spirit0908/STM32/boards/03_can2uart_converter/PCB/can_uart_converter.sch

## KiCad design boards/03_can2uart_converter/PCB/can_uart_converter.sch (2021-06-02)

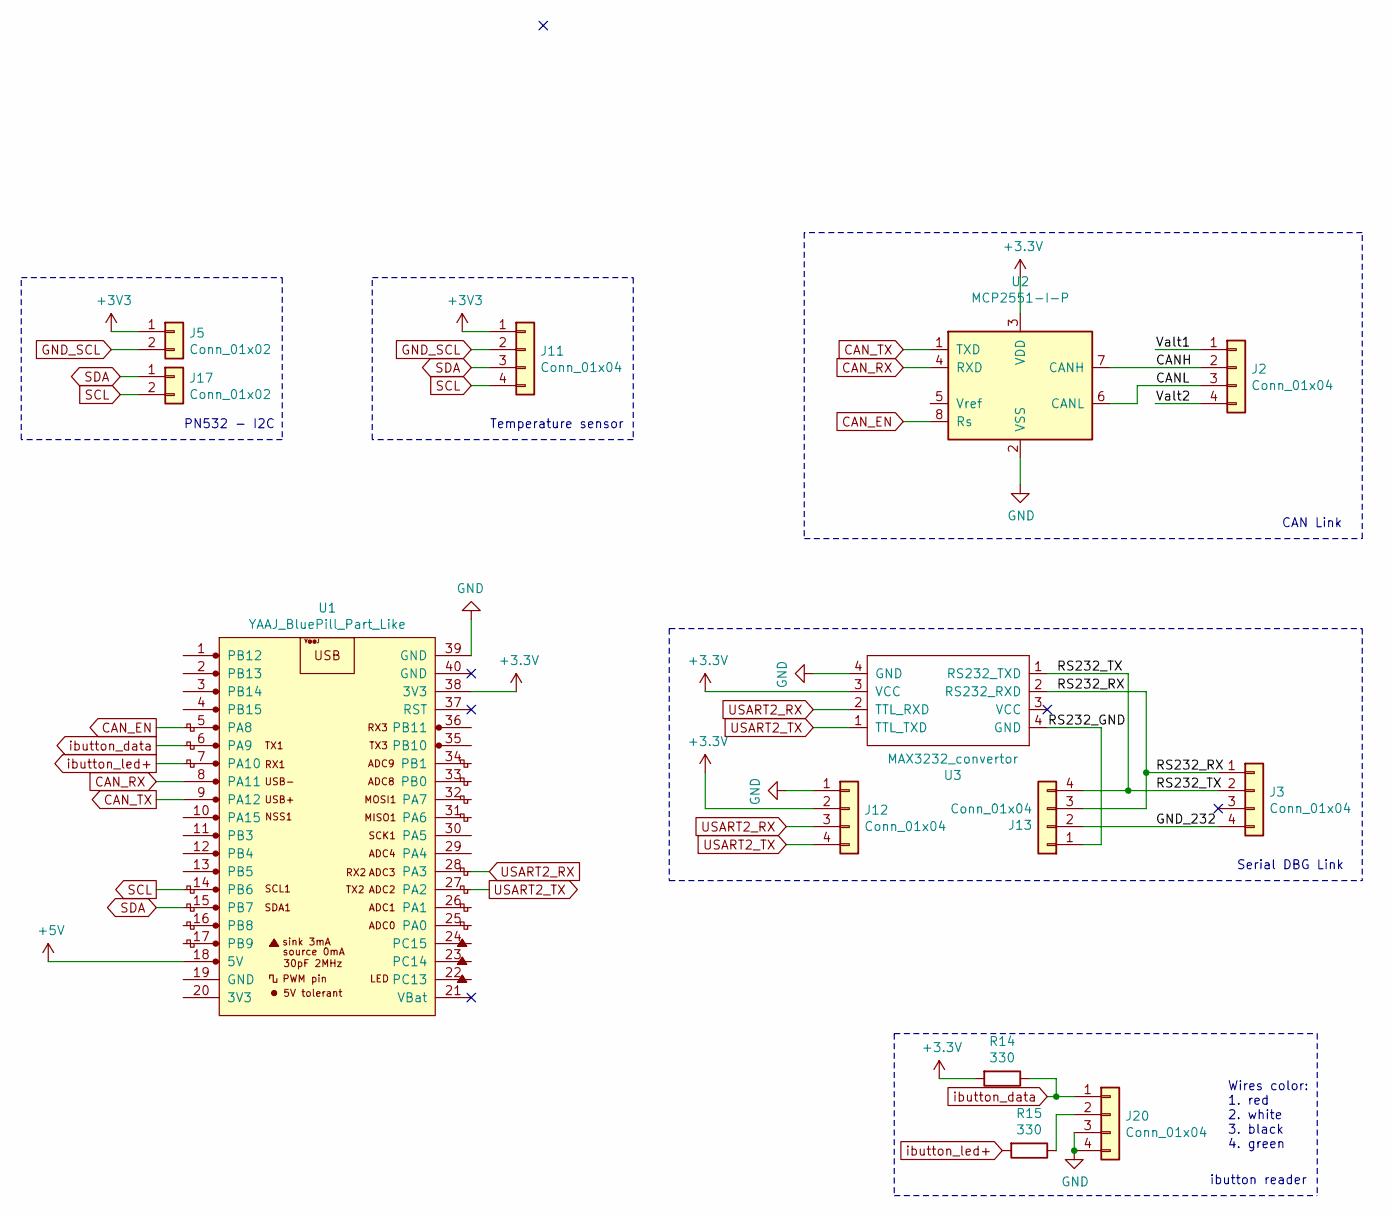
[picture p13: schematic can_uart_converter.sch]

Parts:
J2: Conn_01x04; PinHeader_1x04_P2.54mm_Horizontal
J3, J11, J12, J13, J20: Conn_01x04; PinHeader_1x04_P2.54mm_Vertical
J5, J17: Conn_01x02; PinHeader_1x02_P2.54mm_Vertical
R14, R15: 330; R_Axial_DIN0204_L3.6mm_D1.6mm_P7.62mm_Horizontal
U1: YAAJ_BluePill_Part_Like; YAAJ_BluePill_1
U2: MCP2551-I-P; DIP-8_W7.62mm
U3: MAX3232_convertor

Connections:
+3.3V: J12.2, R14.2, U1.38 (3V3), U2.3 (VDD), U3.3 (VCC)
+3V3: J5.1, J11.1
+5V: U1.18 (5V)
CANH: J2.2, U2.7 (CANH)
CANL: J2.3, U2.6 (CANL)
CAN_EN: U1.5 (PA8), U2.8 (Rs)
CAN_RX: U1.8 (PA11), U2.4 (RXD)
CAN_TX: U1.9 (PA12), U2.1 (TXD)
GND: J12.1, J20.3, J20.4, U1.39 (GND), U2.2 (VSS), U3.4 (GND)
GND_232: J3.4, J13.2
GND_SCL: J5.2, J11.2
unnamed: J20.2, R15.1
RS232_GND: J13.1, U3.4 (GND)
RS232_RX: J3.1, J13.3, U3.2 (RS232_RXD)
RS232_TX: J3.2, J13.4, U3.1 (RS232_TXD)
SCL: J11.4, J17.2, U1.14 (PB6)
SDA: J11.3, J17.1, U1.15 (PB7)
USART2_RX: J12.3, U1.28 (PA3), U3.2 (RS232_RXD)
USART2_TX: J12.4, U1.27 (PA2), U3.1 (RS232_TXD)
Valt1: J2.1
Valt2: J2.4
ibutton_data: J20.1, R14.1, U1.6 (PA9)
ibutton_led+: R15.2, U1.7 (PA10)

Notes on the sheet:
Serial DBG Link
CAN Link
PN532 - I2C
Temperature sensor
ibutton reader
Wires color: 1. red 2. white 3. black 4. green
