spirit0908/STM32/boards/03_can2uart_converter/PCB/ressources.sch

## KiCad design boards/03_can2uart_converter/PCB/ressources.sch (2020-12-13)

Schematic: ressources.sch

Parts:
BZ2: Buzzer; Buzzer_12x9.5RM7.6
J21, J23, J27, J28, J35: Conn_01x02; PinHeader_1x02_P2.54mm_Vertical
J22, J25, J29, J30, J31, J32, J34: Conn_01x04; PinHeader_1x04_P2.54mm_Vertical
J24, J26: Conn_01x03; PinHeader_1x03_P2.54mm_Vertical
J33: DB9_Female; DSUB-9_Female_Horizontal_P2.77x2.84mm_EdgePinOffset4.94mm_H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
J36: Conn_01x04; PinHeader_1x04_P2.54mm_Horizontal
R16, R17, R18, R19, R22, R23, R24: 330; R_Axial_DIN0204_L3.6mm_D1.6mm_P7.62mm_Horizontal
R20: 1.2k; R_Axial_DIN0204_L3.6mm_D1.6mm_P7.62mm_Horizontal
R21: 10k; R_Axial_DIN0204_L3.6mm_D1.6mm_P5.08mm_Horizontal
U10, U11, U12, U13: 4N25; DIP-6_W7.62mm
U14: LTV-814; DIP-4_W7.62mm
U15: MAX3232_convertor
U16: MCP2551-I-P; DIP-8_W7.62mm

Notes on the sheet:
Serial DBG Link
EDF Teleinfo
CAN Link
PN532 - I2C
LED STRIP WHITE
Buzzer
External connectors
Temperature sensor
LED STRIP RGB
Wires color: 1. red 2. white 3. black 4. green
ibutton reader
