spirit0908/STM32/modules/Teleinfo/teleinfo.c

/********************************************************************************
 * File Name          : teleinfo.c
 * Date               : 10/08/2007
 * Description        : Main program body
 *******************************************************************************/

/************************************************************************
* INCLUDES *
************************************************************************/
#include "stm32f10x_lib.h"

#include "stm32f10x_flash.h"
#include "stm32f10x_gpio.h"
#include "stm32f10x_map.h"
#include "stm32f10x_nvic.h"
#include "stm32f10x_rcc.h"
#include "stm32f10x_type.h"
#include "Fifo.h"
#include "teleinfo.h"

/************************************************************************
* DEFINES *
************************************************************************/
#define TIC_FIFO_LENGTH     55

#define MODE1 1
#define MODE2 2
#define TIC_CRC_MODE MODE1


/************************************************************************
* GLOBAL VARIABLES *
************************************************************************/
unsigned char TIC_FIFO_Buff[TIC_FIFO_LENGTH][30];
unsigned char IinstMax=0;

u8 rawDataTab[170];
u16 cptRawData=0;
u8 cptTIC_label=0;

T_TIC_INFO TIC_info;
T_TIC_FIFO TIC_Fifo;

/************************************************************************
* FUNCTIONS *
************************************************************************/

/************************************************************************
 * Function Name  : teleinfo_Init                                       *
 * Input          : None                                                *
 * Output         : None                                                *
 * Return         : None                                                *
 * Description    : Initialize TIC FIFO                                 *
 ************************************************************************/
void teleinfo_Init(void)
{
    /* Initialize Fifo */
    TIC_Fifo.buff       = &(TIC_FIFO_Buff[0][0]);
    TIC_Fifo.size       = TIC_FIFO_LENGTH;
    TIC_Fifo.WriteIdx   = 0;
    TIC_Fifo.ReadIdx    = 0;
    TIC_Fifo.NumElem    = 0;
    TIC_Fifo.NumMaxElem = 0;
    TIC_Fifo.overrun    = 0;
}

/************************************************************************
 * Function Name  : teleinfo_Init                                       *
 * Input          : None                                                *
 * Output         : None                                                *
 * Return         : None                                                *
 * Description    : Initialize TIC FIFO                                 *
 ************************************************************************/
void teleinfo_TIC_reset_values(void)
{
    unsigned char resetStr[13]="-------------";

    /* Reset all options */
    TIC_set_option(ADCO,     resetStr, ADCO_LEN);
    TIC_set_option(OPTARIF,  resetStr, OPTARIF_LEN);
    TIC_set_option(ISOUSC,   resetStr, ISOUSC_LEN);
#if( CBEMM_BASE )
    TIC_set_option(BASE,     resetStr, BASE_LEN);
#endif
#if( CBEMM_HC )
    TIC_set_option(HCHC,     resetStr, HCHC_LEN);
    TIC_set_option(HCHP,     resetStr, HCHP_LEN);
#endif
#if( CBEMM_EJP )
    TIC_set_option(EJPHN,    resetStr, EJPHN_LEN);
    TIC_set_option(EJPHPM,   resetStr, EJPHPM_LEN);
    TIC_set_option(PEJP,     resetStr, PEJP_LEN);
#endif
#if( CBEMM_TEMPO )
    TIC_set_option(BBRHCJB,  resetStr, BBRHCJB_LEN);
    TIC_set_option(BBRHPJB,  resetStr, BBRHPJB_LEN);
    TIC_set_option(BBRHCJW,  resetStr, BBRHCJW_LEN);
    TIC_set_option(BBRHPJW,  resetStr, BBRHPJW_LEN);
    TIC_set_option(BBRHCJR,  resetStr, BBRHCJR_LEN);
    TIC_set_option(BBRHPJR,  resetStr, BBRHPJR_LEN);
    TIC_set_option(DEMAIN,   resetStr, DEMAIN_LEN);
#endif
    TIC_set_option(PTEC,     resetStr, PTEC_LEN);
    TIC_set_option(IINST,    resetStr, IINST_LEN);
    TIC_set_option(ADPS,     resetStr, ADPS_LEN);
    TIC_set_option(IMAX,     resetStr, IMAX_LEN);
    TIC_set_option(PAPP,     resetStr, PAPP_LEN);
    TIC_set_option(HHPHC,    resetStr, HHPHC_LEN);
    TIC_set_option(MOTDETAT, resetStr, MOTDETAT_LEN);
#if( CBETM )
    TIC_set_option(IINST1,   resetStr, IINST1_LEN);
    TIC_set_option(IINST2,   resetStr, IINST2_LEN);
    TIC_set_option(IINST3,   resetStr, IINST3_LEN);
    TIC_set_option(IMAX1,    resetStr, IMAX1_LEN);
    TIC_set_option(IMAX2,    resetStr, IMAX2_LEN);
    TIC_set_option(IMAX3,    resetStr, IMAX3_LEN);
    TIC_set_option(PMAX,     resetStr, PMAX_LEN);
#endif
#if( CBETM_SHORT )
    TIC_set_option(ADIR1,    resetStr, ADIR1_LEN);
    TIC_set_option(ADIR2,    resetStr, ADIR2_LEN);
    TIC_set_option(ADIR3,    resetStr, ADIR3_LEN);
#endif
#if( C_GAZ_AUTRE )
    TIC_set_option(GAZ,      resetStr, GAZ_LEN);
    TIC_set_option(AUTRE,    resetStr, AUTRE_LEN);
#endif
}

/********************************************************************************
 * Function Name  : teleinfo_rawByte_receive                                    *
 * Input          : None                                                        *
 * Output         : None                                                        *
 * Return         : None                                                        *
 * Description    : Add each raw byte received from the TIC device in the FIFO  *
 *                  and split the differents TIC messages. Each element of the  *
 *                  FIFO contain one label with its associated data.            *
 *******************************************************************************/
int teleinfo_rawByte_receive(u8 rawByte)
{
    switch(rawByte)
    {
        case ASCII_LF: /* Start of Label */
            cptTIC_label=0;
            TIC_FIFO_Buff[TIC_Fifo.WriteIdx][cptTIC_label++] = rawByte;
          break;

        case ASCII_CR: /* CR End of label */
          //store and increment fifo
          TIC_FIFO_Buff[TIC_Fifo.WriteIdx][cptTIC_label] = rawByte;

          TIC_Fifo.NumElem++;
          if(TIC_Fifo.NumElem > TIC_Fifo.NumMaxElem ) // For debug purpose
          {
              TIC_Fifo.NumMaxElem = TIC_Fifo.NumElem;
          }

          TIC_Fifo.WriteIdx++;
          if(TIC_Fifo.WriteIdx>=TIC_FIFO_LENGTH)
          {
            TIC_Fifo.WriteIdx=0;
          }
          break;

        case ASCII_STX: //STX Start of Transmission
        case ASCII_ETX: //ETX End of Transmission - !!! if last character was not a CR, label transmission is not complete (telereport access on-going)
          break;

        default:
          //store car
          TIC_FIFO_Buff[TIC_Fifo.WriteIdx][cptTIC_label++] = rawByte;
          break;
    }

    //temporary added for debug:
    if( (rawByte == ASCII_ETX) /*&& (TIC_Fifo.WriteIdx > 30)*/ )
    {
        Teleinfo_Mgt();
    }

    return 0;
}

/********************************************************************************
 * Function Name  : Teleinfo_Mgt                                                *
 * Input          : None                                                        *
 * Output         : None                                                        *
 * Return         : None                                                        *
 * Description    : Check validity for each record of the FIFO                  *
 *******************************************************************************/
void Teleinfo_Mgt(void)
{
    unsigned char label;
    unsigned long int value=0;
    unsigned char WriteIdx = TIC_Fifo.WriteIdx;
    unsigned char *ReadIdx = &(TIC_Fifo.ReadIdx);

    while(*ReadIdx != WriteIdx)
    {
        //check string validity and split values
        if( TIC_check_frame(TIC_FIFO_Buff[*ReadIdx], &label, &value ) )
        {
          //Frame is valid, update info
          if( label != INVALID )
          {
              (void)TIC_FillInInfo(label, value);
          }
        }
        else
        {
            //ignore frame
        }

        // Manage Fifo
        if(TIC_Fifo.NumElem>0)
        {
            TIC_Fifo.NumElem--;
        }

        /* Increment fifo index */
        TIC_Fifo.ReadIdx++;
        if(TIC_Fifo.ReadIdx>=TIC_FIFO_LENGTH)
        {
            TIC_Fifo.ReadIdx=0;
        }
    }
}

/********************************************************************************
 * Function Name  : TIC_check_frame                                             *
 * Input          : str[30]: TIC record in ASCII format                         *
 * Output         : labelCode: label of the record                              *
 *                  valueCode: value of the record                              *
 * Return         : validity of the record:                                     *
 *                   FALSE: record is invalid, record is discarded              *
 *                   TRUE: record is valid and the treatment is done            *
 * Description    : Check validity of a TIC record and split the label and the  *
 *                  value.                                                      *
 *******************************************************************************/
unsigned char TIC_check_frame(unsigned char str[30], unsigned char *labelCode, unsigned long int *labelValue)
{
    unsigned char strLen=0, i, tmp;
    unsigned char labelStr[10], valueStr[12], CRC;
    unsigned char labelLen=0, valueLen=0;

    unsigned char IsValid=FALSE;

    //Read each line received
    if( str[strLen++] == ASCII_LF ) //Check line begins with LF
    {
        /* Get label */
        do
        {
            labelStr[labelLen++] = str[strLen++];
        }
        while( (str[strLen] != ASCII_SP) && (strLen<30) ); //space

        /* Ignore space */
        strLen++;

        /* Get value */
        do
        {
            valueStr[valueLen++] = str[strLen++];
        }
        while( (str[strLen] != ASCII_SP) && (strLen<30) ); //space

        /* Ignore space */
        strLen++;

        /* Get CRC */
        do
        {
            /* 1 byte followed by CR character*/
            CRC = str[strLen++];
        }
        while( (str[strLen] != ASCII_CR) && (strLen<30) ); //CR


        /* Compute and check CRC */
        if( TIC_CRC(str) == CRC )
        {
            /* Convert label to code */
            *labelCode = TIC_getLabelCode(labelStr);

            /* Convert value string to integer*/
            *labelValue = Ascii2Int(valueStr, valueLen);

            if( (*labelCode != INVALID) && (*labelValue != 0) )
            {
                /* Set valid */
                IsValid = TRUE;
            }


            /*ToDo: modify switch case */
            switch (labelStr[0])
            {
                case 'A':
                {
                    //labelCode = IINST;
                    for(i=0; i<valueLen; i++)
                        TIC_info.ADCO[i]=valueStr[i];
                    TIC_info.ADCO[i]='\0';
                }break;

                case 'I':
                {
                    if(labelStr[1] == 'I')
                    {
                        //labelCode = IINST;
                        for(i=0; i<valueLen; i++)
                            TIC_info.IINST[i]=valueStr[i];
                        TIC_info.IINST[i]='\0';

                        /* Update I inst max */
                        tmp=Ascii2Int(valueStr, valueLen);
                        if( tmp > IinstMax )
                        {
                            IinstMax=tmp;
                        }
                    }
                    else if(labelStr[1] == 'M')
                    {
                        //labelCode = IMAX;
                        for(i=0; i<valueLen; i++)
                            TIC_info.IMAX[i]=valueStr[i];
                        TIC_info.IMAX[i]='\0';
                    }
                    else if(labelStr[1] == 'S')
                    {
                        //labelCode = ISOUSC;
                        for(i=0; i<valueLen; i++)
                            TIC_info.ISOUSC[i]=valueStr[i];
                        TIC_info.ISOUSC[i]='\0';
                    }
                    else
                    {
                        //labelCode = INVALID;
                    }
                }break;

                case 'O':
                {
                    //labelCode = OPTARIF;
                    for(i=0; i<valueLen; i++)
                        TIC_info.OPTARIF[i]=valueStr[i];
                    TIC_info.OPTARIF[i]='\0';
                }break;

                case 'H':
                {
                    if(labelStr[3] == 'C')
                    {
                        //labelCode = HCHC;
                        for(i=0; i<valueLen; i++)
                            TIC_info.HCHC[i]=valueStr[i];
                        TIC_info.HCHC[i]='\0';
                    }
                    else if(labelStr[3] == 'P')
                    {
                        //labelCode = HCHP;
                        for(i=0; i<valueLen; i++)
                                TIC_info.HCHP[i]=valueStr[i];
                        TIC_info.HCHP[i]='\0';
                    }
                    else if(labelStr[3] == 'H')
                    {
                        //labelCode = HHPHC;
                        for(i=0; i<valueLen; i++)
                            TIC_info.HHPHC[i]=valueStr[i];
                        TIC_info.HHPHC[i]='\0';
                    }
                    else
                    {
                        //labelCode = INVALID;
                    }
                }break;

                case 'P':
                {
                    if(labelStr[1] == 'T')
                    {
                        //labelCode = PTEC;
                        for(i=0; i<valueLen; i++)
                            TIC_info.PTEC[i]=valueStr[i];
                        TIC_info.PTEC[i]='\0';
                    }
                    else if(labelStr[1] == 'A')
                    {
                        //labelCode = PAPP;
                        for(i=0; i<valueLen; i++)
                            TIC_info.PAPP[i]=valueStr[i];
                        TIC_info.PAPP[i]='\0';
                    }
                }break;

                case 'M':
                {
                    //labelCode = MOTDETAT;
                    for(i=0; i<valueLen; i++)
                        TIC_info.MOTDETAT[i]=valueStr[i];
                    TIC_info.MOTDETAT[i]='\0';
                }break;

                default:
                {
                    //labelCode = INVALID;
                    IsValid = FALSE;
                    //ToDo: Log label and value
                }break;
            }
        }
    }

    return IsValid;
}

/* ToDo: move function in global file */
unsigned char mem_cpy(unsigned char *a, unsigned char *b, unsigned char len)
{
    unsigned char i;
    for(i=0; i<len; i++)
    {
        *a = *b;
        a++;
        b++;
    }
    return 0;
}

unsigned char TIC_set_option(unsigned char option, unsigned char *str, unsigned char len)
{
    unsigned char retVal = 0;
    unsigned char *optionPtr, optionLen;

    switch (option)
    {
        case ADCO:
        {
            optionPtr = TIC_info.ADCO;
            optionLen = ADCO_LEN;
        }break;
        case OPTARIF:
        {
            optionPtr = TIC_info.OPTARIF;
            optionLen = OPTARIF_LEN;
        }break;
        case ISOUSC:
        {
            optionPtr = TIC_info.ISOUSC;
            optionLen = ISOUSC_LEN;
        }break;

#if( CBEMM_BASE )
        case BASE:
        {
            optionPtr = TIC_info.BASE;
            optionLen = BASE_LEN;
        }break;
#endif
#if( CBEMM_HC )
        case HCHC:
        {
            optionPtr = TIC_info.HCHC;
            optionLen = HCHC_LEN;
        }break;
        case HCHP:
        {
            optionPtr = TIC_info.HCHP;
            optionLen = HCHP_LEN;
        }break;
#endif
#if( CBEMM_EJP )
        case EJPHN:
        {
            optionPtr = TIC_info.EJPHN;
            optionLen = EJPHN_LEN;
        }break;
        case EJPHPM:
        {
            optionPtr = TIC_info.EJPHPM;
            optionLen = EJPHPM_LEN;
        }break;
        case PEJP:
        {
            optionPtr = TIC_info.PEJP;
            optionLen = PEJP_LEN;
        }break;
#endif
#if( CBEMM_TEMPO )
    case BBRHCJB:
        {
            optionPtr = TIC_info.BBRHCJB;
            optionLen = BBRHCJB_LEN;
        }break;
        case BBRHPJB:
        {
            optionPtr = TIC_info.BBRHPJB;
            optionLen = BBRHPJB_LEN;
        }break;
        case BBRHCJW:
        {
            optionPtr = TIC_info.BBRHCJW;
            optionLen = BBRHCJW_LEN;
        }break;
        case BBRHPJW:
        {
            optionPtr = TIC_info.BBRHPJW;
            optionLen = BBRHPJW_LEN;
        }break;
        case BBRHCJR:
        {
            optionPtr = TIC_info.BBRHCJR;
            optionLen = BBRHCJR_LEN;
        }break;
        case BBRHPJR:
        {
            optionPtr = TIC_info.BBRHPJR;
            optionLen = BBRHPJR_LEN;
        }break;
        case DEMAIN:
        {
            optionPtr = TIC_info.DEMAIN;
            optionLen = DEMAIN_LEN;
        }break;
#endif
        case PTEC:
        {
            optionPtr = TIC_info.PTEC;
            optionLen = PTEC_LEN;
        }break;
        case IINST:
        {
            optionPtr = TIC_info.IINST;
            optionLen = IINST_LEN;
        }break;
        case ADPS:
        {
            optionPtr = TIC_info.ADPS;
            optionLen = ADPS_LEN;
        }break;
        case IMAX:
        {
            optionPtr = TIC_info.IMAX;
            optionLen = IMAX_LEN;
        }break;
        case PAPP:
        {
            optionPtr = TIC_info.PAPP;
            optionLen = PAPP_LEN;
        }break;
        case HHPHC:
        {
            optionPtr = TIC_info.HHPHC;
            optionLen = HHPHC_LEN;
        }break;
        case MOTDETAT:
        {
            optionPtr = TIC_info.MOTDETAT;
            optionLen = MOTDETAT_LEN;
        }break;
#if( CBETM )
        case IINST1:
        {
            optionPtr = TIC_info.IINST1;
            optionLen = IINST1_LEN;
        }break;
        case IINST2:
        {
            optionPtr = TIC_info.IINST2;
            optionLen = IINST2_LEN;
        }break;
        case IINST3:
        {
            optionPtr = TIC_info.IINST3;
            optionLen = IINST3_LEN;
        }break;
        case IMAX1:
        {
            optionPtr = TIC_info.IMAX1;
            optionLen = IMAX1_LEN;
        }break;
        case IMAX2:
        {
            optionPtr = TIC_info.IMAX2;
            optionLen = IMAX2_LEN;
        }break;
        case IMAX3:
        {
            optionPtr = TIC_info.IMAX3;
            optionLen = IMAX3_LEN;
        }break;
        case PMAX:
        {
            optionPtr = TIC_info.PMAX;
            optionLen = PMAX_LEN;
        }break;
#endif
#if( CBETM_SHORT )
        case ADIR1:
        {
            optionPtr = TIC_info.ADIR1;
            optionLen = ADIR1_LEN;
        }break;
        case ADIR2:
        {
            optionPtr = TIC_info.ADIR2;
            optionLen = ADIR2_LEN;
        }break;
        case ADIR3:
        {
            optionPtr = TIC_info.ADIR3;
            optionLen = ADIR3_LEN;
        }break;
#endif
#if( C_GAZ_AUTRE )
        case GAZ:
        {
            optionPtr = TIC_info.GAZ;
            optionLen = GAZ_LEN;
        }break;
        case AUTRE:
        {
            optionPtr = TIC_info.AUTRE;
            optionLen = AUTRE_LEN;
        }break;
#endif
        default:
        {
            retVal = 1 /*NOK*/;
        }break;
    }

    if(len == optionLen)
    {
        mem_cpy(optionPtr, str, len);
    }
    else
    {
        /* ERROR */
        /* Incorrect option len */
        retVal = 1;
    }

    return retVal;
}

unsigned char TIC_get_option(unsigned char option, unsigned char *str, unsigned char len)
{
    unsigned char retVal = 0;
    unsigned char *optionPtr, optionLen;
    
    switch (option)
    {
        case ADCO:
        {
            optionPtr = TIC_info.ADCO;
            optionLen = ADCO_LEN;
        }break;
        case OPTARIF:
        {
            optionPtr = TIC_info.OPTARIF;
            optionLen = OPTARIF_LEN;
        }break;
        case ISOUSC:
        {
            optionPtr = TIC_info.ISOUSC;
            optionLen = ISOUSC_LEN;
        }break;

#if( CBEMM_BASE )
        case BASE:
        {
            optionPtr = TIC_info.BASE;
            optionLen = BASE_LEN;
        }break;
#endif
#if( CBEMM_HC )
        case HCHC:
        {
            optionPtr = TIC_info.HCHC;
            optionLen = HCHC_LEN;
        }break;
        case HCHP:
        {
            optionPtr = TIC_info.HCHP;
            optionLen = HCHP_LEN;
        }break;
#endif
#if( CBEMM_EJP )
        case EJPHN:
        {
            optionPtr = TIC_info.EJPHN;
            optionLen = EJPHN_LEN;
        }break;
        case EJPHPM:
        {
            optionPtr = TIC_info.EJPHPM;
            optionLen = EJPHPM_LEN;
        }break;
        case PEJP:
        {
            optionPtr = TIC_info.PEJP;
            optionLen = PEJP_LEN;
        }break;
#endif
#if( CBEMM_TEMPO )
    case BBRHCJB:
        {
            optionPtr = TIC_info.BBRHCJB;
            optionLen = BBRHCJB_LEN;
        }break;
        case BBRHPJB:
        {
            optionPtr = TIC_info.BBRHPJB;
            optionLen = BBRHPJB_LEN;
        }break;
        case BBRHCJW:
        {
            optionPtr = TIC_info.BBRHCJW;
            optionLen = BBRHCJW_LEN;
        }break;
        case BBRHPJW:
        {
            optionPtr = TIC_info.BBRHPJW;
            optionLen = BBRHPJW_LEN;
        }break;
        case BBRHCJR:
        {
            optionPtr = TIC_info.BBRHCJR;
            optionLen = BBRHCJR_LEN;
        }break;
        case BBRHPJR:
        {
            optionPtr = TIC_info.BBRHPJR;
            optionLen = BBRHPJR_LEN;
        }break;
        case DEMAIN:
        {
            optionPtr = TIC_info.DEMAIN;
            optionLen = DEMAIN_LEN;
        }break;
#endif
        case PTEC:
        {
            optionPtr = TIC_info.PTEC;
            optionLen = PTEC_LEN;
        }break;
        case IINST:
        {
            optionPtr = TIC_info.IINST;
            optionLen = IINST_LEN;
        }break;
        case ADPS:
        {
            optionPtr = TIC_info.ADPS;
            optionLen = ADPS_LEN;
        }break;
        case IMAX:
        {
            optionPtr = TIC_info.IMAX;
            optionLen = IMAX_LEN;
        }break;
        case PAPP:
        {
            optionPtr = TIC_info.PAPP;
            optionLen = PAPP_LEN;
        }break;
        case HHPHC:
        {
            optionPtr = TIC_info.HHPHC;
            optionLen = HHPHC_LEN;
        }break;
        case MOTDETAT:
        {
            optionPtr = TIC_info.MOTDETAT;
            optionLen = MOTDETAT_LEN;
        }break;
#if( CBETM )
        case IINST1:
        {
            optionPtr = TIC_info.IINST1;
            optionLen = IINST1_LEN;
        }break;
        case IINST2:
        {
            optionPtr = TIC_info.IINST2;
            optionLen = IINST2_LEN;
        }break;
        case IINST3:
        {
            optionPtr = TIC_info.IINST3;
            optionLen = IINST3_LEN;
        }break;
        case IMAX1:
        {
            optionPtr = TIC_info.IMAX1;
            optionLen = IMAX1_LEN;
        }break;
        case IMAX2:
        {
            optionPtr = TIC_info.IMAX2;
            optionLen = IMAX2_LEN;
        }break;
        case IMAX3:
        {
            optionPtr = TIC_info.IMAX3;
            optionLen = IMAX3_LEN;
        }break;
        case PMAX:
        {
            optionPtr = TIC_info.PMAX;
            optionLen = PMAX_LEN;
        }break;
#endif
#if( CBETM_SHORT )
        case ADIR1:
        {
            optionPtr = TIC_info.ADIR1;
            optionLen = ADIR1_LEN;
        }break;
        case ADIR2:
        {
            optionPtr = TIC_info.ADIR2;
            optionLen = ADIR2_LEN;
        }break;
        case ADIR3:
        {
            optionPtr = TIC_info.ADIR3;
            optionLen = ADIR3_LEN;
        }break;
#endif
#if( C_GAZ_AUTRE )
        case GAZ:
        {
            optionPtr = TIC_info.GAZ;
            optionLen = GAZ_LEN;
        }break;
        case AUTRE:
        {
            optionPtr = TIC_info.AUTRE;
            optionLen = AUTRE_LEN;
        }break;
#endif
        default:
        {
            retVal = 1 /*NOK*/;
        }break;
    }

    if(retVal == 0)
    {
        if(len == optionLen)
        {
            mem_cpy(str, optionPtr, optionLen);
        }
        else
        {
            retVal = 1;
        }
    }
    
    return retVal;
}

/********************************************************************************
 * Function Name  : Ascii2Int                                                   *
 * Input          : *str: string containing the ASCII format number             *
 *                  len: length of the ASCII string                             *
 * Output         : None                                                        *
 * Return         : Number in integer format                                    *
 * Description    : Convert a number in ASCII format to an integer value        *
 *******************************************************************************/
unsigned long int Ascii2Int(unsigned char *str, unsigned char len)
{
    unsigned char i;
    unsigned long int tmp=0;

    for(i=0; i<len; i++)
    {
        if( ((str[i] >= 'A') && (str[i]<='Z')) ||
            ((str[i] >= 'a') && (str[i]<='z')) )
        {
            tmp = tmp*10;
            tmp += ( str[i] - 48 );
        }
        else
        {
            tmp = 0;
            break;
        }
    }

    return tmp;
}

/*******************************************************************************
 * Function Name  : TIC_FillInInfo                                             *
 * Input          : labelCode: label extracted from a record                   *
 *                  val: value associated to the label                         *
 * Output         : None                                                       *
 * Return         : Status of the operation                                    *
 * Description    :                                                            *
 ******************************************************************************/
unsigned char TIC_FillInInfo(unsigned char labelCode, unsigned int val)
{
//  switch (labelCode)
//  {
//  case ADCO:
//      TIC_info.ADCO = val;
//      break;


//	case 'A': //ADCO
////                  labelCode = ADCO;
//                    for(i=0; i<valueLen; i++)
//                        TIC_info.ADCO[i]=valueStr[i];
//                    TIC_info.ADCO[i]='\0';
//                break;


//  case OPTARIF:
//      TIC_info.OPTARIF = val;
//      break;
//  case ISOUSC:
//      TIC_info.ISOUSC = val;
//      break;
//  case HCHC:
//	  if( TIC_info.HCHC > val)
//	  {
//		  //error: current index is greater than the read index
//	  }
//	  TIC_info.HCHC = val;
//      break;
//  case HCHP:
//	  if( TIC_info.HCHP > val)
//	  {
//		  //error: current index is greater than the read index
//	  }
//      TIC_info.HCHP = val;
//      break;
//  case PTEC:
//	  if( TIC_info.PTEC > val)
//	  {
//		  //error: current index is greater than the read index
//	  }
//	  TIC_info.PTEC = val;
//      break;
//  case IINST:
//      TIC_info.IINST = val;
//      break;
//  case IMAX:
//      TIC_info.IMAX = val;
//      break;
//  case PAPP:
//      TIC_info.PAPP = val;
//      break;
//  case HHPHC:
//      TIC_info.HHPHC = val;
//      break;
//  case MOTDETAT:
//      // ToDo: Inform application about a change in the MOTDETAT
//	  TIC_info.MOTDETAT = val;
//      break;
//  }
    return 0;
}

/*******************************************************************************
 * Function Name  : TIC_getLabelCode                                           *
 * Input          : str: string containing the label                           *
 * Output         : None                                                       *
 * Return         : Label code                                                 *
 * Description    : Get the code associated to a label                         *
 ******************************************************************************/
unsigned char TIC_getLabelCode(unsigned char str[5])
{
    unsigned char labelCode;

    switch (str[0])
    {
        case 'A': //ADCO
            labelCode = ADCO;
        break;

        case 'I':
            if(str[1] == 'I')
                labelCode = IINST;
            else if(str[1] == 'M')
                labelCode = IMAX;
            else if(str[1] == 'S')
                labelCode = ISOUSC;
            else
                labelCode = INVALID;
        break;

        case 'O':
            labelCode = OPTARIF;
        break;

        case 'H':
            if(str[3] == 'C')
                labelCode = HCHC;
            else if(str[3] == 'P')
                labelCode = HCHP;
            else if(str[3] == 'H')
                labelCode = HHPHC;
            else
                labelCode = INVALID;
            break;

        case 'P':
            if(str[1] == 'T')
                labelCode = PTEC;
            else if(str[1] == 'A')
                labelCode = PAPP;
            break;

        case 'M':
            labelCode = MOTDETAT;
            break;

        default:
            labelCode = INVALID;
            break;
    }

    return labelCode;
}

/*******************************************************************************
 * Function Name  : TTIC_CRC                                                   *
 * Input          : str: record in string format, containing the label and     *
 *                  the associated value                                       *
 * Output         : None                                                       *
 * Return         : Checksum value of the record                               *
 * Description    : Calculate the checksum of a TIC record                     *
 ******************************************************************************/
unsigned char TIC_CRC(unsigned char *str)
{
    /* CRC is computed from the input string by summing up each byte of the string.
     * Depending on the mode, the following characters are taken into account:
     * in mode 1: LABEL + SP + DATA
     * in mode 2: LABEL + SP + DATA + SP
     */
    unsigned char tmp=0, i, sp=0;

    // Compute CRC from string (only LowByte is kept)
    for(i=0; i<30; i++)
    {
        if(str[i] == ASCII_LF) //Beginning of the string
        {
            tmp=0;
        }
        else if( (str[i] == ASCII_SP) && (sp==0)) //End of label
        {
            tmp += str[i];
            sp++;
        }
        else if(str[i] == ASCII_SP) //End of value
        {
#if TIC_CRC_MODE == MODE2
            // In mode 2, add compute CRC with CR
            tmp += str[i];
#endif
            break;
        }
        else if( (str[i] == ASCII_CR) || (str[i] == ASCII_ETX) ) //End if string
        {
            //Error case: End of string reached.
            break;
        }
        else
        {
            tmp += str[i];
        }
    }

    /* Mask with 0x3F */
    tmp &= 0x3F;

    /* Add 0x20 to display ASCII character */
    tmp += 0x20;

    return tmp;
}

/*******************************************************************************
 * Function Name  : Teleinfo_USART_Init                                        *
 * Input          : USART module to initialize                                 *
 * Output         : None                                                       *
 * Return         : None                                                       *
 * Description    : Initialize USART link to be used with EDF smart meters     *
 ******************************************************************************/
void Teleinfo_USART_Init(USART_TypeDef* USARTx)
{
    USART_InitTypeDef USART_InitStruct;

    /* Enable USART  */
    USART_InitStruct.USART_BaudRate     = 0x04B0; /* 1200 Baud */
    USART_InitStruct.USART_WordLength   = USART_WordLength_8b;
    USART_InitStruct.USART_StopBits     = USART_StopBits_1;
    USART_InitStruct.USART_Parity       = USART_Parity_Even;
    USART_InitStruct.USART_HardwareFlowControl = USART_HardwareFlowControl_None;
    USART_InitStruct.USART_Mode         = USART_Mode_Rx;    /* Only Rx pin is enabled */
    USART_InitStruct.USART_Clock        = USART_Clock_Disable;
    USART_InitStruct.USART_CPOL         = USART_CPOL_Low;
    USART_InitStruct.USART_CPHA         = USART_CPHA_1Edge;
    USART_InitStruct.USART_LastBit      = USART_LastBit_Disable;

    USART_Cmd(USARTx, ENABLE);
    USART_Init(USARTx, &USART_InitStruct);

    /* Enable IT on USART handler */
    USART_ITConfig(USARTx, USART_IT_RXNE, DISABLE);
    USART_ITConfig(USARTx, USART_IT_TXE, DISABLE);
    USART_ITConfig(USARTx, USART_IT_TC, DISABLE);
}
