spirit0908/STM32/modules/nokia/n3310.h

#ifndef _N3310_H_
#define _N3310_H_

#include "stm32f10x_lib.h"
#include "stm32f10x_gpio.h"

// Port Pins
#define LCD_PORT				GPIOB
#define LCD_DC_PIN				GPIO_Pin_14
#define LCD_CE_PIN				GPIO_Pin_13
#define LCD_RST_PIN				GPIO_Pin_12
#define LCD_SDIN_PIN			GPIO_Pin_15
#define LCD_SCLK_PIN			GPIO_Pin_3

#define SET_DC					GPIO_SetBits(LCD_PORT, LCD_DC_PIN)
#define RESET_DC				GPIO_ResetBits(LCD_PORT, LCD_DC_PIN)

#define SET_CE					GPIO_SetBits(LCD_PORT, LCD_CE_PIN)
#define RESET_CE				GPIO_ResetBits(LCD_PORT, LCD_CE_PIN)

#define SET_RST					GPIO_SetBits(LCD_PORT, LCD_RST_PIN)
#define RESET_RST				GPIO_ResetBits(LCD_PORT, LCD_RST_PIN)

#define SET_SDIN				GPIO_SetBits(LCD_PORT, LCD_SDIN_PIN)
#define RESET_SDIN				GPIO_ResetBits(LCD_PORT, LCD_SDIN_PIN)

#define SET_SCLK				GPIO_SetBits(LCD_PORT, LCD_SCLK_PIN)
#define RESET_SCLK				GPIO_ResetBits(LCD_PORT, LCD_SCLK_PIN)

// Display resolution
#define LCD_X_RES                  84 // horizontal
#define LCD_Y_RES                  48 // vertical

// Cache size ( 84 * 48 ) / 8 = 504
#define LCD_CACHE_SIZE             ( ( LCD_X_RES * LCD_Y_RES ) / 8 )

// Return value
#define OK                         0   // OK
#define OUT_OF_BORDER              1   // Out of border
#define OK_WITH_WRAP               2   // Wraped

typedef enum
{
    LCD_CMD  = 0,     // Command
    LCD_DATA = 1      // Data

} LcdCmdData;

typedef enum
{
    PIXEL_OFF =  0,   // On
    PIXEL_ON  =  1,   // Off
    PIXEL_XOR =  2    // Invert

} LcdPixelMode;

typedef enum
{
    FONT_1X = 0,      // Small font size
    FONT_2X = 1,      // Big font size
    FONT_4X = 2       // Large font size (fon numbert only)
} LcdFontSize;

void LcdInit(void);
void LcdClear(void);
void LcdUpdate(void);
void LcdImage(const unsigned char *imageData );
void LcdContrast(unsigned char contrast);
unsigned char LcdGotoXYFont(unsigned char x, unsigned char y );
unsigned char LcdChr(LcdFontSize size, unsigned char ch );
unsigned char LcdStr(LcdFontSize size, unsigned char dataArray[]);
unsigned char LcdFStr(LcdFontSize size, const unsigned char *dataPtr);
unsigned char LcdPixel(unsigned char x, unsigned char y, LcdPixelMode mode);
unsigned char LcdLine(unsigned char x1, unsigned char y1, unsigned char x2, unsigned char y2, LcdPixelMode mode);
unsigned char LcdCircle(unsigned char x, unsigned char y, unsigned char radius, LcdPixelMode mode);
unsigned char LcdRect(unsigned char x1, unsigned char y1, unsigned char x2, unsigned char y2, LcdPixelMode mode );
void LcdWriteToCache(int addr, unsigned char data);
void LcdIvertLine(unsigned char line);
void LcdIvertLineFragment(unsigned char line, unsigned char chr_x1, unsigned char chr_x2);

// Symbols table ASCII[0x20-0x7F] + CP1251[0xC0-0xFF]
static const unsigned char FontLookup [][5] =
{
   { 0x00, 0x00, 0x00, 0x00, 0x00 },   //   0x20  32
   { 0x00, 0x00, 0x5F, 0x00, 0x00 },   // ! 0x21  33
   { 0x00, 0x07, 0x00, 0x07, 0x00 },   // " 0x22  34
   { 0x14, 0x7F, 0x14, 0x7F, 0x14 },   // # 0x23  35
   { 0x24, 0x2A, 0x7F, 0x2A, 0x12 },   // $ 0x24  36
   { 0x4C, 0x2C, 0x10, 0x68, 0x64 },   // % 0x25  37
   { 0x36, 0x49, 0x55, 0x22, 0x50 },   // & 0x26  38
   { 0x00, 0x05, 0x03, 0x00, 0x00 },   // ' 0x27  39
   { 0x00, 0x1C, 0x22, 0x41, 0x00 },   // ( 0x28  40
   { 0x00, 0x41, 0x22, 0x1C, 0x00 },   // ) 0x29  41
   { 0x14, 0x08, 0x3E, 0x08, 0x14 },   // * 0x2A  42
   { 0x08, 0x08, 0x3E, 0x08, 0x08 },   // + 0x2B  43
   { 0x00, 0x00, 0x50, 0x30, 0x00 },   // , 0x2C  44
   { 0x10, 0x10, 0x10, 0x10, 0x10 },   // - 0x2D  45
   { 0x00, 0x60, 0x60, 0x00, 0x00 },   // . 0x2E  46
   { 0x20, 0x10, 0x08, 0x04, 0x02 },   // / 0x2F  47
   { 0x3E, 0x51, 0x49, 0x45, 0x3E },   // 0 0x30  48
   { 0x00, 0x42, 0x7F, 0x40, 0x00 },   // 1 0x31  49
   { 0x42, 0x61, 0x51, 0x49, 0x46 },   // 2 0x32  50
   { 0x21, 0x41, 0x45, 0x4B, 0x31 },   // 3 0x33  51
   { 0x18, 0x14, 0x12, 0x7F, 0x10 },   // 4 0x34  52
   { 0x27, 0x45, 0x45, 0x45, 0x39 },   // 5 0x35  53
   { 0x3C, 0x4A, 0x49, 0x49, 0x30 },   // 6 0x36  54
   { 0x01, 0x71, 0x09, 0x05, 0x03 },   // 7 0x37  55
   { 0x36, 0x49, 0x49, 0x49, 0x36 },   // 8 0x38  56
   { 0x06, 0x49, 0x49, 0x29, 0x1E },   // 9 0x39  57
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
};


#endif  /*  _N3310_H_ */
