spirit0908/STM32/modules/LedStrip/LedStrip.h

/************************************************************************
 * File Name          : LedStrip.h
 * Author             :
 * Date               : 17/10/2018
 * Description        : header template file
 ***********************************************************************/

#ifndef LEDSTRIP_H_
#define LEDSTRIP_H_

/************************************************************************
* INCLUDES *
************************************************************************/


/************************************************************************
* DEFINES *
************************************************************************/


/************************************************************************
* STRUCTURES *
************************************************************************/


/************************************************************************
* GLOBAL VARIABLES *
************************************************************************/


/************************************************************************
* FUNCTIONS PROTOTYPE *
************************************************************************/
void LedStrip_Mgt(void);


#endif /* LEDSTRIP_H_ */
