spirit0908/STM32/boards/01_stm_proto_board_V2/stm_proto/Core/Inc/uart2can.h

/************************************************************************
 * File Name          : templace_header.h
 * Author             : author
 * Date               : 23/02/2020
 * Description        : header template file
 ***********************************************************************/

#ifndef UART2CAN_HEADER_H_
#define UART2CAN_HEADER_H_


/************************************************************************
* INCLUDES *
************************************************************************/


/************************************************************************
* MACROS *
************************************************************************/


/************************************************************************
* STRUCTURES *
************************************************************************/


/************************************************************************
* GLOBAL VARIABLES *
************************************************************************/


/************************************************************************
* FUNCTIONS PROTOTYPE *
************************************************************************/


#endif /* UART2CAN_HEADER_H_ */
