spirit0908/STM32/modules/Light/Light_cfg.c

/************************************************************************
 * File Name          : Light_cfg.c
 * Author             :
 * Date               : 26/02/2021
 * Description        :
 ***********************************************************************/

/************************************************************************
* INCLUDES *
************************************************************************/
//#include "Light_cfg.h"
#include "Light.h"


/************************************************************************v
* DEFINES *
************************************************************************/


/************************************************************************
* GLOBAL VARIABLES *
************************************************************************/
T_LightConfig LightConfig[MAX_LIGHT_NUM]=
{
    /* Port | Pin | type */
    { GPIOB , GPIO_PIN_13, 0b00001000, 0, 0 },
    { GPIOB , GPIO_PIN_14, 0b00001000, 0, 0 },
    { GPIOB , GPIO_PIN_15, 0b00001000, 0, 0 }
};

T_LightState LightState[MAX_LIGHT_NUM]=
{
    /* state | order */
    {0, 0, 0, 0},
    {0, 0, 0, 0},
    {0, 0, 0, 0}
};

/************************************************************************
* FUNCTIONS *
************************************************************************/
