spirit0908/STM32/modules/Light/Light_cfg.h

/************************************************************************
 * File Name          : Light.h
 * Author             :
 * Date               : 12/02/2017
 * Description        : header template file
 ***********************************************************************/

#ifndef LIGHT_CFG_H
#define LIGHT_CFG_H

/************************************************************************
* INCLUDES *
************************************************************************/
//#include "stm32f10x_lib.h"
//#include "stm32f10x_map.h"
//#include "stm32f10x_gpio.h"
#include <main.h>

/************************************************************************
* MACROS *
************************************************************************/

enum
{
    Light_ID_0 = 0,
    Light_ID_1,
    Light_ID_2,
    // Keep this position
    Light_ID_MAX
};
#define MAX_LIGHT_NUM Light_ID_MAX


/************************************************************************
* STRUCTURES *
************************************************************************/


/************************************************************************
* GLOBAL VARIABLES *
************************************************************************/


/************************************************************************
* FUNCTIONS PROTOTYPE *
************************************************************************/

#endif  /* LIGHT_CFG_H */
