spirit0908/STM32/boards/01_stm_proto_board_V2/stm_proto/Core/Inc/Task.h

/************************************************************************
 * File Name          : Task.h
 * Author             : author
 * Date               : 12/02/2017
 * Description        : header template file
 ***********************************************************************/
#ifndef TASK_H
#define TASK_H

/************************************************************************
* INCLUDES *
************************************************************************/


/************************************************************************
* DEFINES *
************************************************************************/
#define SYNC_TASK  0
#define ASYNC_TASK 1


/************************************************************************
* STRUCTURES *
************************************************************************/
typedef enum
{
    TASK_STOPPED = 0,
    TASK_WAITING = 1,
    TASK_PENDING = 2,
    TASK_RUNNING = 3,
    TASK_ERROR = 4
}T_task_state;


typedef struct      
{
    unsigned char (*pf)();  // pointer to task
    T_task_state  state ;   // Current state of the task
    unsigned int cpt ;      // Current function executed in the task
    unsigned char sync_type;// sync or async task
    unsigned long periodicity;  // Periodicity of the task (10ms, 20ms, 50ms...)
    unsigned int offset;    //offset
} T_TASK ;


typedef struct
{
    unsigned char * TList; 
    unsigned char pFirst;
    unsigned char pLast;
    unsigned char nbElem;
    unsigned char maxNumElem; //used for debug purposes
    unsigned char overrun;
}T_TASK_LIST;


/************************************************************************
* GLOBAL VARIABLES *
************************************************************************/


/************************************************************************
* FUNCTIONS PROTOTYPE *
************************************************************************/
void TaskManager_Init();
void TaskManager(void);
void TaskAdd(unsigned char TaskId);
void TaskAdd_unique(unsigned char TaskId);
unsigned char TaskGet(unsigned char *TaskId);
void Task_Manager_IT(void);


#endif  /* TASK_H */
