spirit0908/STM32/modules/Light/tests/main.h

#define GPIO_PIN_13 13
#define GPIO_PIN_14 14
#define GPIO_PIN_15 15

#define GPIOA        1
#define GPIOB        2
#define GPIOC        3
