spirit0908/STM32/modules/Teleinfo/tests/stubs.c

#include "stm32f10x_usart.h"

void USART_Init(USART_TypeDef* USARTx, USART_InitTypeDef* USART_InitStruct)
{
}

void USART_ITConfig(USART_TypeDef* USARTx, u16 USART_IT, FunctionalState NewState)
{
}

void USART_Cmd(USART_TypeDef* USARTx, FunctionalState NewState)
{
}
